JasonKamps/loadshedding-clock/3D/sign/NOT LOADSHEDDING.png

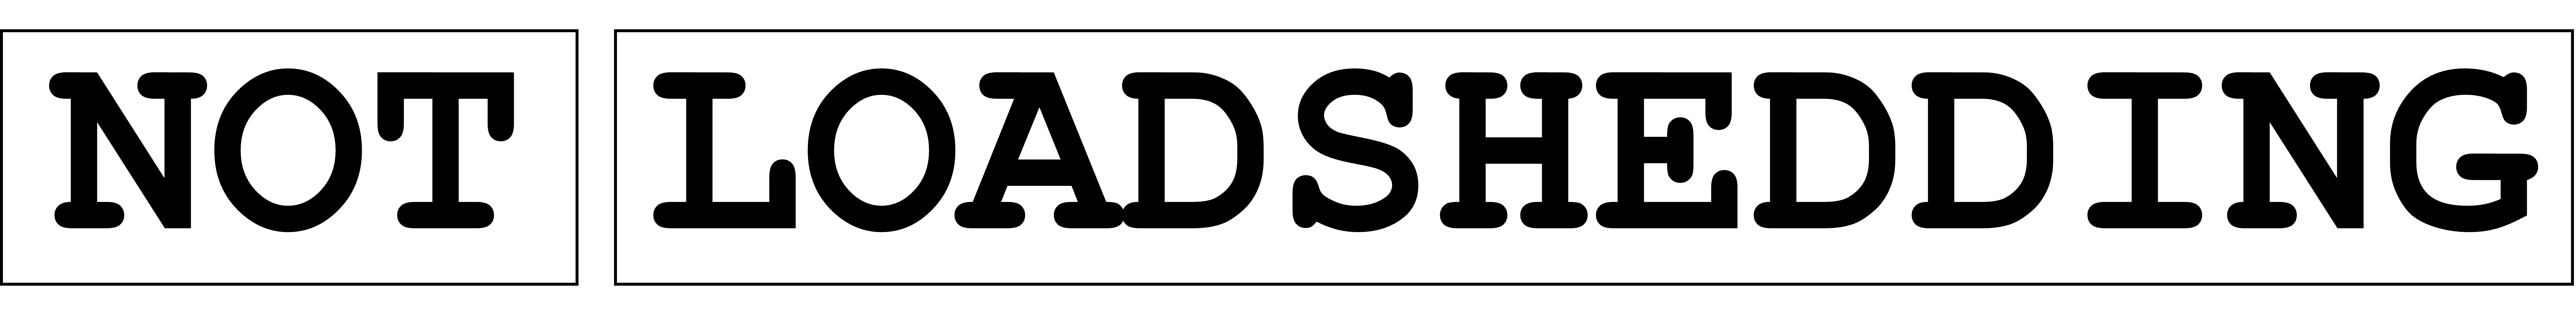
3D/sign/NOT LOADSHEDDING.png
