JasonKamps/loadshedding-clock/PCB/loadshedding.kicad_sch

## KiCad design PCB/loadshedding.kicad_sch (2024-01-03)

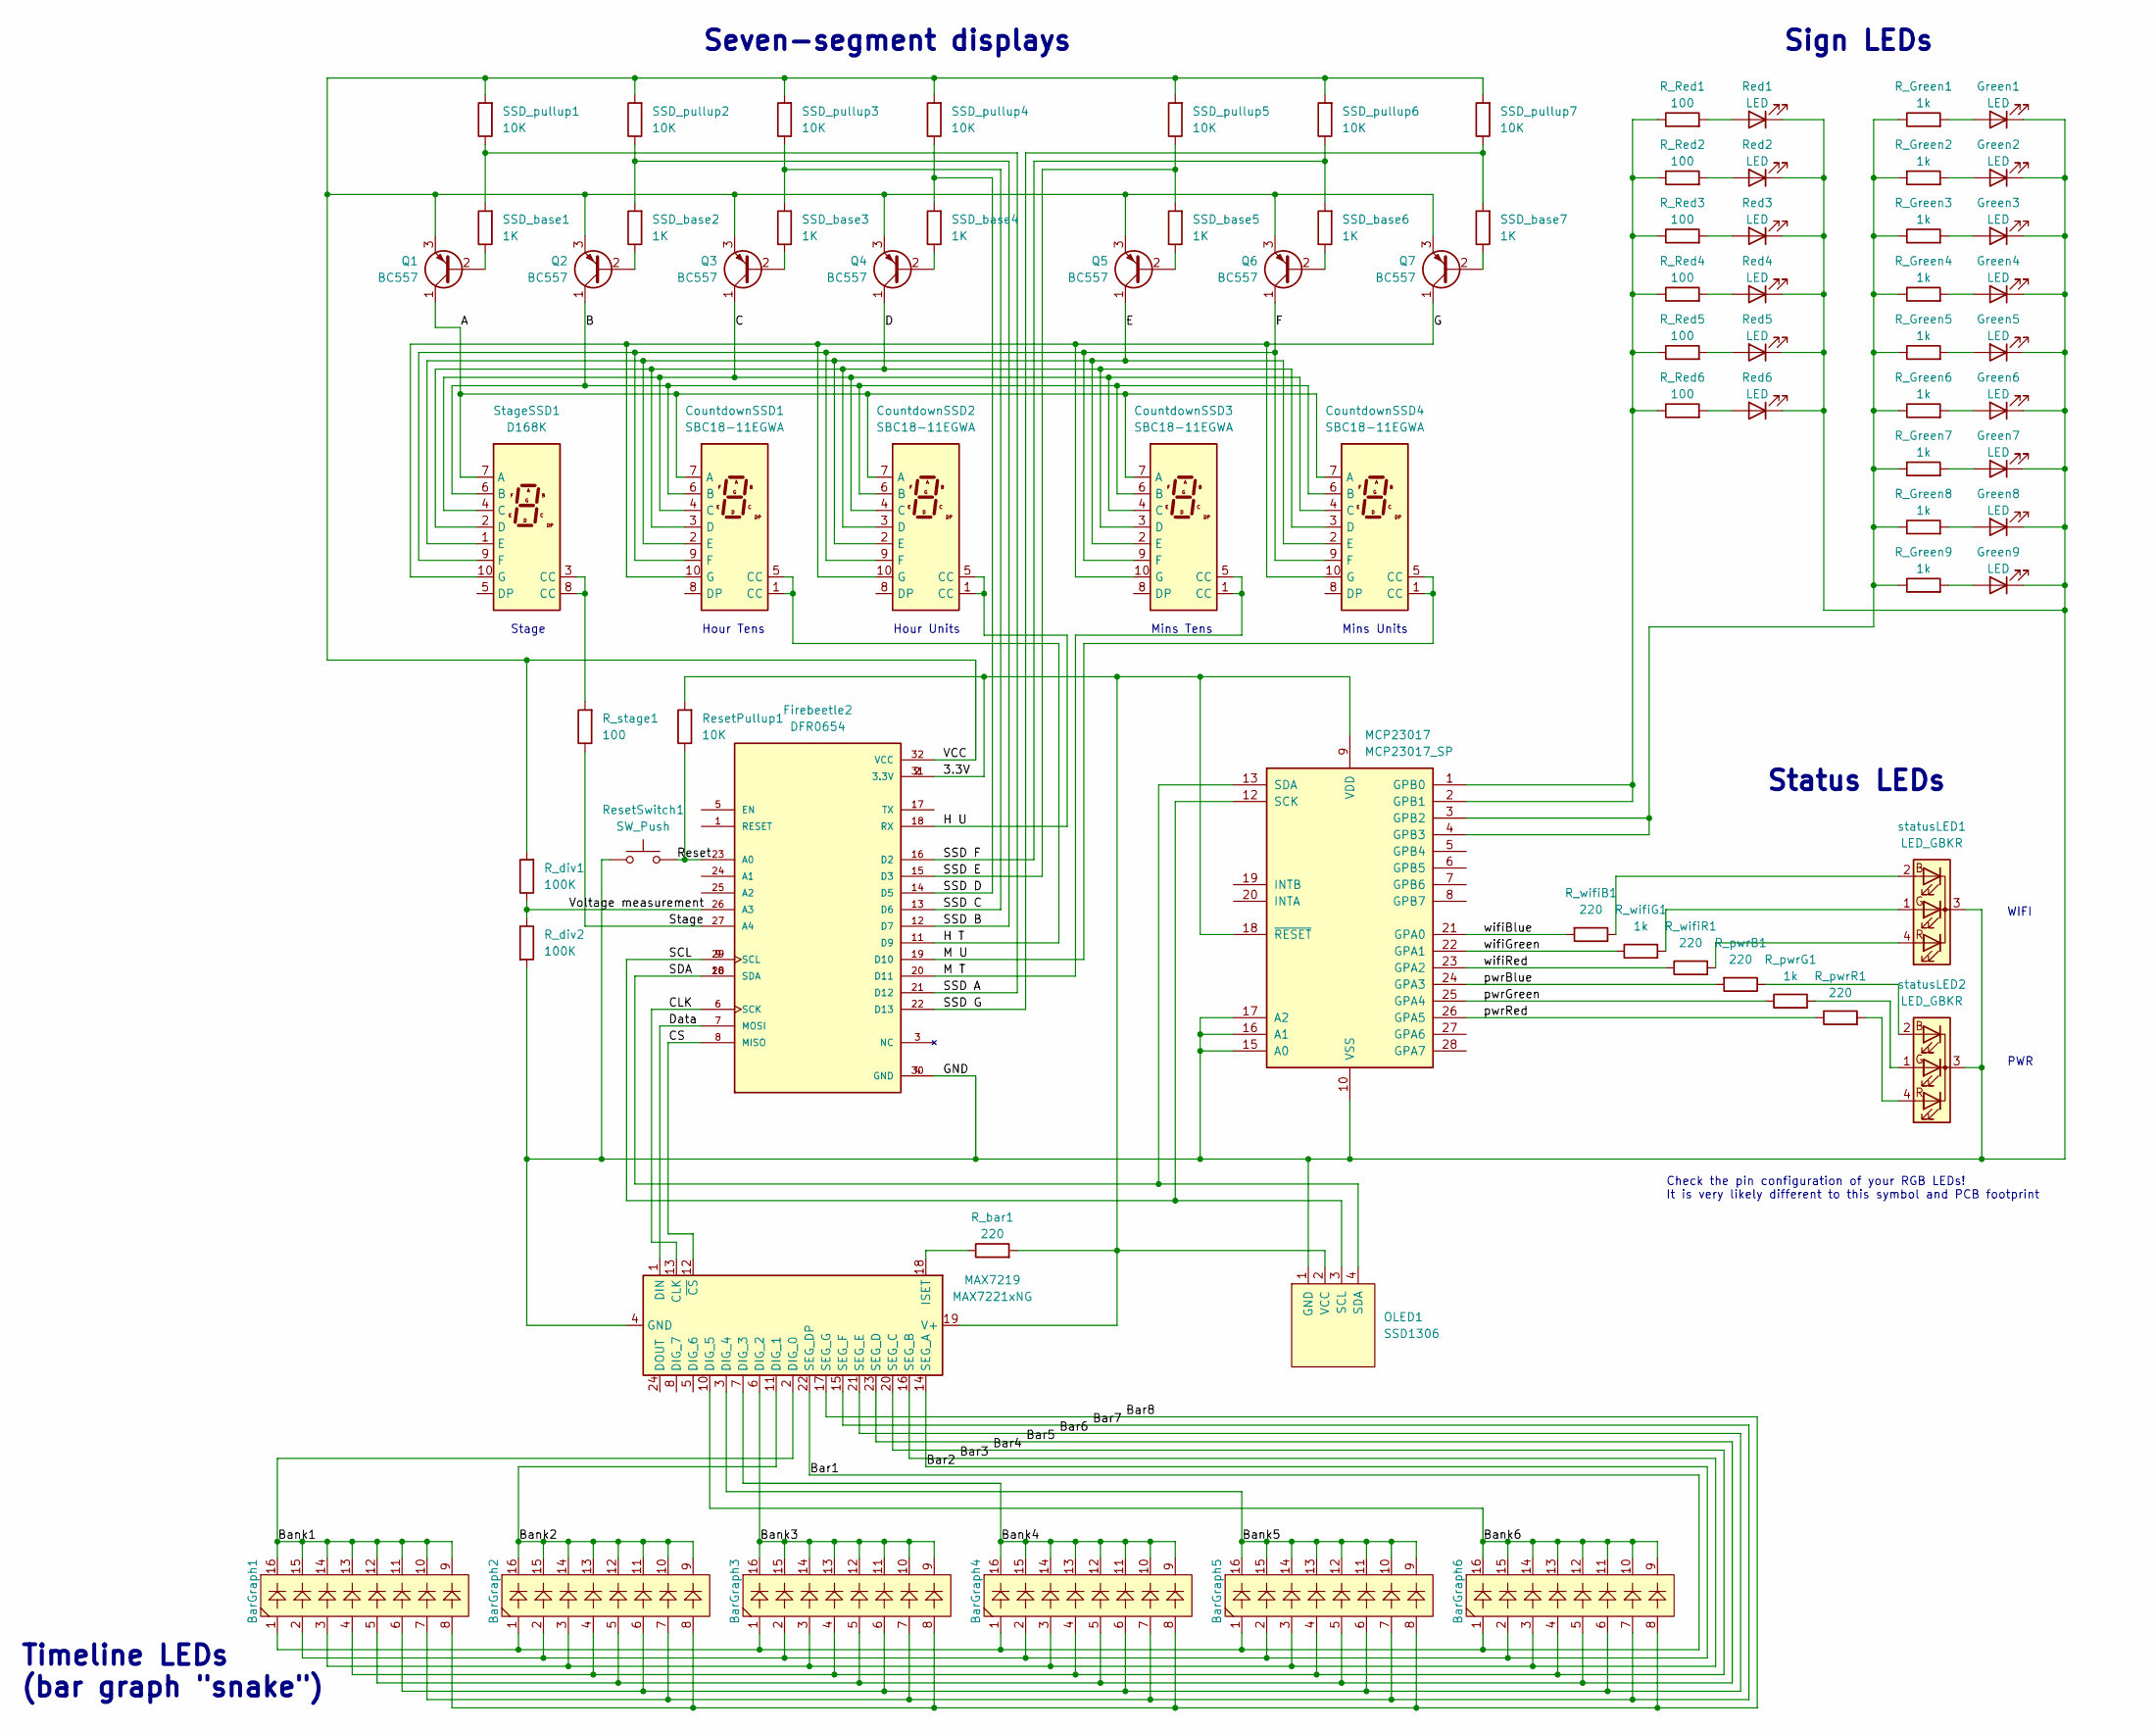
[picture p19: schematic loadshedding.kicad_sch]

Parts:
BarGraph1, BarGraph2, BarGraph3, BarGraph4, BarGraph5, BarGraph6: Bar graph
CountdownSSD1, CountdownSSD2, CountdownSSD3, CountdownSSD4: SBC18-11EGWA; SBC18-11SURKCGKWA
Firebeetle2: DFR0654; MODULE_DFR0654
Green1, Green2, Green3, Green4, Green5, Green6, Green7, Green8, Green9: LED; LED_D5.0mm
MAX7219: MAX7221xNG; DIP-24_W7.62mm
MCP23017: MCP23017_SP; DIP-28_W7.62mm
OLED1: SSD1306; oled
Q1, Q2, Q3, Q4, Q5, Q6, Q7: BC557; TO-92_Inline
R_Green1, R_Green2, R_Green3, R_Green4, R_Green5, R_Green6, R_Green7, R_Green8, R_Green9: 1k; R_Axial_DIN0207_L6.3mm_D2.5mm_P10.16mm_Horizontal
R_Red1, R_Red2, R_Red3, R_Red4, R_Red5, R_Red6: 100; R_Axial_DIN0207_L6.3mm_D2.5mm_P10.16mm_Horizontal
R_bar1: 220; R_Axial_DIN0207_L6.3mm_D2.5mm_P10.16mm_Horizontal
R_div1, R_div2: 100K; R_Axial_DIN0207_L6.3mm_D2.5mm_P10.16mm_Horizontal
R_pwrB1: 220; R_Axial_DIN0207_L6.3mm_D2.5mm_P10.16mm_Horizontal
R_pwrG1: 1k; R_Axial_DIN0207_L6.3mm_D2.5mm_P10.16mm_Horizontal
R_pwrR1: 220; R_Axial_DIN0207_L6.3mm_D2.5mm_P10.16mm_Horizontal
R_stage1: 100; R_Axial_DIN0207_L6.3mm_D2.5mm_P10.16mm_Horizontal
R_wifiB1: 220; R_Axial_DIN0207_L6.3mm_D2.5mm_P10.16mm_Horizontal
R_wifiG1: 1k; R_Axial_DIN0207_L6.3mm_D2.5mm_P10.16mm_Horizontal
R_wifiR1: 220; R_Axial_DIN0207_L6.3mm_D2.5mm_P10.16mm_Horizontal
Red1, Red2, Red3, Red4, Red5, Red6: LED; LED_D5.0mm
ResetPullup1: 10K; R_Axial_DIN0207_L6.3mm_D2.5mm_P10.16mm_Horizontal
ResetSwitch1: SW_Push; SW_PUSH_6mm
SSD_base1, SSD_base2, SSD_base3, SSD_base4, SSD_base5, SSD_base6, SSD_base7: 1K; R_Axial_DIN0207_L6.3mm_D2.5mm_P10.16mm_Horizontal
SSD_pullup1, SSD_pullup2, SSD_pullup3, SSD_pullup4, SSD_pullup5, SSD_pullup6, SSD_pullup7: 10K; R_Axial_DIN0207_L6.3mm_D2.5mm_P10.16mm_Horizontal
StageSSD1: D168K; D1X8K
statusLED1, statusLED2: LED_GBKR; LED_D5.0mm-4_RGB_Wide_Pins

Connections:
3.3V: Firebeetle2.2 (3.3V), Firebeetle2.31 (3.3V), MAX7219.19 (V+), MCP23017.9 (VDD), MCP23017.18 (~RESET), OLED1.2 (VCC), R_bar1.2, ResetPullup1.2
A: CountdownSSD1.7 (A), CountdownSSD2.7 (A), CountdownSSD3.7 (A), CountdownSSD4.7 (A), Q1.1 (C), StageSSD1.7 (A)
B: CountdownSSD1.6 (B), CountdownSSD2.6 (B), CountdownSSD3.6 (B), CountdownSSD4.6 (B), Q2.1 (C), StageSSD1.6 (B)
Bank1: BarGraph1.9, BarGraph1.10, BarGraph1.11, BarGraph1.12, BarGraph1.13, BarGraph1.14, BarGraph1.15, BarGraph1.16, MAX7219.2 (DIG_0)
Bank2: BarGraph2.9, BarGraph2.10, BarGraph2.11, BarGraph2.12, BarGraph2.13, BarGraph2.14, BarGraph2.15, BarGraph2.16, MAX7219.11 (DIG_1)
Bank3: BarGraph3.9, BarGraph3.10, BarGraph3.11, BarGraph3.12, BarGraph3.13, BarGraph3.14, BarGraph3.15, BarGraph3.16, MAX7219.6 (DIG_2)
Bank4: BarGraph4.9, BarGraph4.10, BarGraph4.11, BarGraph4.12, BarGraph4.13, BarGraph4.14, BarGraph4.15, BarGraph4.16, MAX7219.7 (DIG_3)
Bank5: BarGraph5.9, BarGraph5.10, BarGraph5.11, BarGraph5.12, BarGraph5.13, BarGraph5.14, BarGraph5.15, BarGraph5.16, MAX7219.3 (DIG_4)
Bank6: BarGraph6.9, BarGraph6.10, BarGraph6.11, BarGraph6.12, BarGraph6.13, BarGraph6.14, BarGraph6.15, BarGraph6.16, MAX7219.10 (DIG_5)
Bar1: BarGraph1.1, BarGraph2.1, BarGraph3.1, BarGraph4.1, BarGraph5.1, BarGraph6.1, MAX7219.22 (SEG_DP)
Bar2: BarGraph1.2, BarGraph2.2, BarGraph3.2, BarGraph4.2, BarGraph5.2, BarGraph6.2, MAX7219.14 (SEG_A)
Bar3: BarGraph1.3, BarGraph2.3, BarGraph3.3, BarGraph4.3, BarGraph5.3, BarGraph6.3, MAX7219.16 (SEG_B)
Bar4: BarGraph1.4, BarGraph2.4, BarGraph3.4, BarGraph4.4, BarGraph5.4, BarGraph6.4, MAX7219.20 (SEG_C)
Bar5: BarGraph1.5, BarGraph2.5, BarGraph3.5, BarGraph4.5, BarGraph5.5, BarGraph6.5, MAX7219.23 (SEG_D)
Bar6: BarGraph1.6, BarGraph2.6, BarGraph3.6, BarGraph4.6, BarGraph5.6, BarGraph6.6, MAX7219.21 (SEG_E)
Bar7: BarGraph1.7, BarGraph2.7, BarGraph3.7, BarGraph4.7, BarGraph5.7, BarGraph6.7, MAX7219.15 (SEG_F)
Bar8: BarGraph1.8, BarGraph2.8, BarGraph3.8, BarGraph4.8, BarGraph5.8, BarGraph6.8, MAX7219.17 (SEG_G)
C: CountdownSSD1.4 (C), CountdownSSD2.4 (C), CountdownSSD3.4 (C), CountdownSSD4.4 (C), Q3.1 (C), StageSSD1.4 (C)
CLK: Firebeetle2.6 (SCK), MAX7219.13 (CLK)
CS: Firebeetle2.8 (MISO), MAX7219.12 (~CS)
D: CountdownSSD1.3 (D), CountdownSSD2.3 (D), CountdownSSD3.3 (D), CountdownSSD4.3 (D), Q4.1 (C), StageSSD1.2 (D)
Data: Firebeetle2.7 (MOSI), MAX7219.1 (DIN)
E: CountdownSSD1.2 (E), CountdownSSD2.2 (E), CountdownSSD3.2 (E), CountdownSSD4.2 (E), Q5.1 (C), StageSSD1.1 (E)
F: CountdownSSD1.9 (F), CountdownSSD2.9 (F), CountdownSSD3.9 (F), CountdownSSD4.9 (F), Q6.1 (C), StageSSD1.9 (F)
G: CountdownSSD1.10 (G), CountdownSSD2.10 (G), CountdownSSD3.10 (G), CountdownSSD4.10 (G), Q7.1 (C), StageSSD1.10 (G)
GND: Firebeetle2.4 (GND), Firebeetle2.30 (GND), Green1.1 (K), Green2.1 (K), Green3.1 (K), Green4.1 (K), Green5.1 (K), Green6.1 (K), Green7.1 (K), Green8.1 (K), Green9.1 (K), MAX7219.4 (GND), MAX7219.9 (GND), MCP23017.10 (VSS), MCP23017.15 (A0), MCP23017.16 (A1), MCP23017.17 (A2), OLED1.1 (GND), R_div2.2, Red1.1 (K), Red2.1 (K), Red3.1 (K), Red4.1 (K), Red5.1 (K), Red6.1 (K), ResetSwitch1.1, statusLED1.3 (K), statusLED2.3 (K)
H T: CountdownSSD1.1 (CC), CountdownSSD1.5 (CC), Firebeetle2.11 (D9)
H U: CountdownSSD2.1 (CC), CountdownSSD2.5 (CC), Firebeetle2.18 (RX)
M T: CountdownSSD3.1 (CC), CountdownSSD3.5 (CC), Firebeetle2.20 (D11)
M U: CountdownSSD4.1 (CC), CountdownSSD4.5 (CC), Firebeetle2.19 (D10)
unnamed: Green1.2 (A), R_Green1.2
unnamed: Green2.2 (A), R_Green2.2
unnamed: Green3.2 (A), R_Green3.2
unnamed: Green4.2 (A), R_Green4.2
unnamed: Green5.2 (A), R_Green5.2
unnamed: Green6.2 (A), R_Green6.2
unnamed: Green7.2 (A), R_Green7.2
unnamed: Green8.2 (A), R_Green8.2
unnamed: Green9.2 (A), R_Green9.2
unnamed: MAX7219.18 (ISET), R_bar1.1
unnamed: MCP23017.1 (GPB0), MCP23017.2 (GPB1), R_Red1.1, R_Red2.1, R_Red3.1, R_Red4.1, R_Red5.1, R_Red6.1
unnamed: MCP23017.3 (GPB2), MCP23017.4 (GPB3), R_Green1.1, R_Green2.1, R_Green3.1, R_Green4.1, R_Green5.1, R_Green6.1, R_Green7.1, R_Green8.1, R_Green9.1
unnamed: Q1.2 (B), SSD_base1.1
unnamed: Q2.2 (B), SSD_base2.1
unnamed: Q3.2 (B), SSD_base3.1
unnamed: Q4.2 (B), SSD_base4.1
unnamed: Q5.2 (B), SSD_base5.1
unnamed: Q6.2 (B), SSD_base6.1
unnamed: Q7.2 (B), SSD_base7.1
unnamed: R_Red1.2, Red1.2 (A)
unnamed: R_Red2.2, Red2.2 (A)
unnamed: R_Red3.2, Red3.2 (A)
unnamed: R_Red4.2, Red4.2 (A)
unnamed: R_Red5.2, Red5.2 (A)
unnamed: R_Red6.2, Red6.2 (A)
unnamed: R_pwrB1.1, statusLED2.2 (BA)
unnamed: R_pwrG1.2, statusLED2.1 (GA)
unnamed: R_pwrR1.2, statusLED2.4 (RA)
unnamed: R_stage1.2, StageSSD1.3 (CC), StageSSD1.8 (CC)
unnamed: R_wifiB1.1, statusLED1.2 (BA)
unnamed: R_wifiG1.2, statusLED1.1 (GA)
unnamed: R_wifiR1.2, statusLED1.4 (RA)
Reset: Firebeetle2.23 (A0), ResetPullup1.1, ResetSwitch1.2
SCL: Firebeetle2.9 (SCL), Firebeetle2.29 (SCL), MCP23017.12 (SCK), OLED1.3 (SCL)
SDA: Firebeetle2.10 (SDA), Firebeetle2.28 (SDA), MCP23017.13 (SDA), OLED1.4 (SDA)
SSD A: Firebeetle2.21 (D12), SSD_base1.2, SSD_pullup1.1
SSD B: Firebeetle2.12 (D7), SSD_base2.2, SSD_pullup2.1
SSD C: Firebeetle2.13 (D6), SSD_base3.2, SSD_pullup3.1
SSD D: Firebeetle2.14 (D5), SSD_base4.2, SSD_pullup4.1
SSD E: Firebeetle2.15 (D3), SSD_base5.2, SSD_pullup5.1
SSD F: Firebeetle2.16 (D2), SSD_base6.2, SSD_pullup6.1
SSD G: Firebeetle2.22 (D13), SSD_base7.2, SSD_pullup7.1
Stage: Firebeetle2.27 (A4), R_stage1.1
VCC: Firebeetle2.32 (VCC), Q1.3 (E), Q2.3 (E), Q3.3 (E), Q4.3 (E), Q5.3 (E), Q6.3 (E), Q7.3 (E), R_div1.2, SSD_pullup1.2, SSD_pullup2.2, SSD_pullup3.2, SSD_pullup4.2, SSD_pullup5.2, SSD_pullup6.2, SSD_pullup7.2
Voltage measurement: Firebeetle2.26 (A3), R_div1.1, R_div2.1
pwrBlue: MCP23017.24 (GPA3), R_pwrB1.2
pwrGreen: MCP23017.25 (GPA4), R_pwrG1.1
pwrRed: MCP23017.26 (GPA5), R_pwrR1.1
wifiBlue: MCP23017.21 (GPA0), R_wifiB1.2
wifiGreen: MCP23017.22 (GPA1), R_wifiG1.1
wifiRed: MCP23017.23 (GPA2), R_wifiR1.1

Notes on the sheet:
Mins Units
Seven-segment displays
Timeline LEDs (bar graph "snake")
Mins Tens
Sign LEDs
Status LEDs
Hour Units
Stage
Hour Tens
Check the pin configuration of your RGB LEDs! It is very likely different to this symbol and PCB footprint
WIFI
PWR
