JasonKamps/loadshedding-clock/loadshedding-clock-code/src/connectWiFi.h

#ifndef CONNECTWIFI_H
#define CONNECTWIFI_H

#include "Arduino.h"
#include <WiFiManager.h> // https://github.com/tzapu/WiFiManager
#include "oled.h"
#include "storage.h"

boolean setupWiFi();
void resetWiFi();
boolean isWiFiConnected();

#endif
