JasonKamps/loadshedding-clock/loadshedding-clock-code/src/timeline.h

#ifndef TIMELINE_H
#define TIMELINE_H

#include "Arduino.h"
#include "Schedule.h"
#include <MD_MAX72xx.h>
#include <SPI.h>

void setupTimeline();
void updateTimeline(Schedule schedule);
void updateTimelineWithEvent(Event event);
void setLED(int index);
void clearLED(int index);
bool getLEDStatus(int index);
void clearTimelineLEDs();
void sweepTimelineLEDs();
void flashCurrentTimelineLED();

#endif
