JasonKamps/loadshedding-clock/loadshedding-clock-code/src/api.h

#ifndef API_H
#define API_H

#include "Arduino.h"
#include <HTTPClient.h>
#include <ArduinoJson.h> // https://github.com/bblanchon/ArduinoJson
#include "time.h"
#include "storage.h"

void retrieveArea();
void retrieveEvents();
int getAllowanceUsage();

#endif
